ClockWorks001/PIC16F1827_MelodyTimer4/PIC16F1827_MelodyTimer4.X/vClock01.c

/*************************************************
*  clock01
*************************************************/
#define CLOCK01_LIB

#include <xc.h>         // XC8 General Include File
#include "vClock01.h"

/*******************************
*  clear clock01 parameter
*******************************/
void vClock01_Clear()
{
	s1mSecc = 0;
	cFlagSec = 0;
	ucSec01= ucMin01= ucHour01=0;
}

/*******************************
*  user interrupt work
*  call this work evry 1msec interrupt.
*******************************/
void vClock01_interrupt()
{
    // for Timer1 interrupted
    cFlag1mSec = 1;
    s10mSecc++;
    if(s10mSecc >= 10 ){        // 1msec * 10 = 10msec
            s10mSecc = 0;
            cFlag10mSec++;
    }
    s1mSecc++;
    if(s1mSecc >= 1000 ){	// 1msec * 1000 = 1sec
            s1mSecc = 0;
            cFlagSec++;
    }
}

/*******************************
*  check & clear 2msec count
*******************************/
char cFlag1mSec_ON()
{
    if(cFlag1mSec >= 1){
            cFlag1mSec = 0;
            return 1;
    } else {
            return 0;
    }

}

/*******************************
*  check & clear 10msec count
*******************************/
char cFlag10mSec_ON()
{
    if(cFlag10mSec >= 1){
            cFlag10mSec = 0;
            return 1;
    } else {
            return 0;
    }

}

/*******************************
*  Timer count
*******************************/
void vClock01()
{

	if(cFlagSec) {				// 1sec passing
		ucSec01 += cFlagSec;		// add 1 sec
		cFlagSec = 0;
		if(ucSec01 > 59){			// 1 minute passing
			ucSec01 = 0;
			ucMin01++;			// add 1 minute

			cMinCountDown--;		// count down 1 minute

			if(ucMin01 > 59){
				ucMin01 = 0;
				ucHour01++;		// 1 hour passing
				if(ucHour01 > 23){
					ucHour01 = 0;
				}
			}

		}

	}
}

/*******************************
*  vSetMinCountDownTime
*******************************/
void vSetMinCountDownTime(char cTime)
{
    cMinCountDown = cTime;
}

/*******************************
*  cIsMinCountDownTimeZero
*******************************/
char cIsMinCountDownTimeZero()
{
    if(cMinCountDown <= 0) {
        return 1;
    }else{
        return 0;
    }
}

/*******************************
*  cIsMinCountDownTimeZero
*******************************/
char cGetMinCountDownTime()
{
        return cMinCountDown;
}

/*******************************
*  ucGetMin01
*******************************/
unsigned char ucGetMin01()
{
        return ucMin01;
}

/*******************************
*  ucGetMin01
*******************************/
short sGet1mSecc()
{
        return s1mSecc;
}
