ClockWorks001/PIC16F1827_MelodyTimer4/PIC16F1827_MelodyTimer4.X/vInteger.h

/*-------------------------------------------*/
/* Integer type definitions for FatFs module */
/*-------------------------------------------*/
#ifndef _INTEGER
#define _INTEGER

/* These types must be 16-bit, 32-bit or larger integer */
typedef int				INT;
typedef unsigned int	UINT;

/* These types must be 8-bit integer */
//typedef char			CHAR;
typedef unsigned char	UCHAR;
typedef unsigned char	BYTE;

/* These types must be 16-bit integer */
typedef short			SHORT;
typedef unsigned short	USHORT;
typedef unsigned short	WORD;
typedef unsigned short	WCHAR;

/* These types must be 32-bit integer */
//typedef long			LONG;
//typedef unsigned long	ULONG;
//typedef unsigned long	DWORD;

#endif
